i-Saac-IV/micro-affirmations/media/DSC01120.JPG

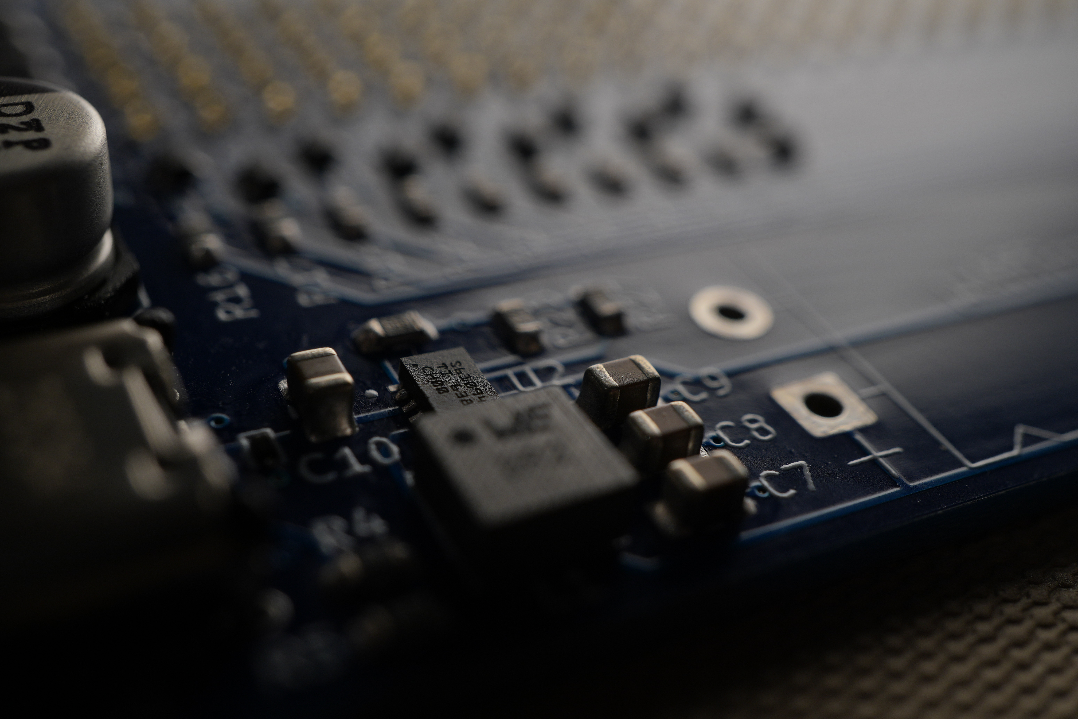
media/DSC01120.JPG
