i-Saac-IV/micro-affirmations/Core/Src/messages.c

/*

File:   messages.c
Author: Isaac Pawley

*/

#include "messages.h"

#ifndef __weak
#define __weak __attribute__((weak))
#endif

__weak const char *messages[] = {
    "uAffirmations - A microcontroller-based affection-giving MACHINE!",
    "Whoops, it looks like you forgot to add your own messages!",
    "!\"#$%&'()*+,-./0123456789:;<=>?@ABCDEFGHIJKLMNOPQRSTUVWXYZ[\\]^_`abcdefghijklmnopqrstuvwxyz{|}~"
};

__weak size_t number_of_messages = sizeof(messages) / sizeof(messages[0]);
