i-Saac-IV/micro-affirmations/Core/Inc/bitmaps.h

/*

File:   bitmaps.h
Author: Isaac Pawley

*/

#ifndef INC_BITMAPS_H_
#define INC_BITMAPS_H_

#include <stdint.h>

extern const uint8_t battery_20x5[];
extern const uint8_t heart_5x5[];
extern const uint8_t heartFilled_5x5[];

#endif /* INC_BITMAPS_H_ */
