i-Saac-IV/micro-affirmations/Core/Src/bitmaps.c

/*

File:   bitmaps.c
Author: Isaac Pawley

*/

#include "bitmaps.h"

const uint8_t battery_20x5[] = {
    0xFF, 0xFF, 0xE0,
    0x80, 0x00, 0x30,
    0x80, 0x00, 0x10,
    0x80, 0x00, 0x30,
    0xFF, 0xFF, 0xE0
};

const uint8_t heart_5x5[] = {
    0x50,
    0xA8,
    0x88,
    0x50,
    0x20
};

const uint8_t heartFilled_5x5[] = {
    0x50,
    0xF8,
    0xF8,
    0x70,
    0x20
};
